duwaar/Pocket-Color-Sensor/calibration/blue_1.csv

num | red | green | blue
0 | 6179 | 1407 | 683
1 | 6105 | 1406 | 669
2 | 6119 | 1404 | 675
3 | 6107 | 1406 | 669
4 | 6121 | 1411 | 677
5 | 6073 | 1400 | 677
6 | 6146 | 1410 | 685
7 | 6099 | 1418 | 683
8 | 6130 | 1409 | 668
9 | 6092 | 1413 | 679
10 | 6123 | 1409 | 683
11 | 6112 | 1398 | 671
12 | 6114 | 1410 | 684
13 | 6094 | 1411 | 683
14 | 6142 | 1411 | 668
15 | 6131 | 1417 | 684
16 | 6114 | 1411 | 679
17 | 6126 | 1411 | 683
18 | 6110 | 1413 | 683
19 | 6093 | 1399 | 677
20 | 6141 | 1406 | 685
21 | 6109 | 1413 | 676
22 | 6164 | 1415 | 685
23 | 6152 | 1405 | 668
24 | 6161 | 1406 | 679
25 | 6150 | 1409 | 670
26 | 6139 | 1412 | 678
27 | 6131 | 1411 | 677
28 | 6141 | 1411 | 679
29 | 6139 | 1412 | 676
30 | 6134 | 1407 | 678
31 | 6149 | 1407 | 677
32 | 6106 | 1418 | 685
33 | 6201 | 1412 | 685
34 | 6143 | 1420 | 684
35 | 6178 | 1411 | 685
36 | 6154 | 1420 | 684
37 | 6197 | 1412 | 684
38 | 6160 | 1421 | 685
39 | 6132 | 1414 | 671
40 | 6172 | 1400 | 685
41 | 6144 | 1419 | 681
42 | 6160 | 1412 | 678
43 | 6164 | 1407 | 675
44 | 6146 | 1402 | 670
45 | 6166 | 1406 | 668
46 | 6152 | 1408 | 679
47 | 6156 | 1412 | 675
48 | 6148 | 1404 | 678
49 | 6186 | 1406 | 669
50 | 6147 | 1409 | 676
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
